impatrq/ojo_de_van_gogh/Docs/README.md

### Documentación

#### Este modulo esta divido de las siguientes partes:

* **Carpeta Tecnica**: dentro de esta carpeta esta la documentación técnica del proyecto. Aquí podemos encontrar la información de la *versión estable* del sistema y ver en mucho detalle que hace el proyecto, como lo hace y por que lo hace. Dentro de este archivo no hay ideas experimentales sino que **todo lo que se escribió esta comprobado que funciona**
* **Carpeta de Campo**: dentro de estar carpeta esta la documentación de campo. Aqui podemos encontrar la tracción del proyecto, teniendo la posibilidad de recapitular los errores que fueron surgiendo y como se solucionar
* **Entrevistas**: dentro de esta carpeta están las entrevistas que realizamos con personas con discapacidad visual para validar si nuestro producto es factible de tener una inserción en el mercado
