impatrq/ojo_de_van_gogh/Docs/Encuestas/Encuesta _Mitrovich.md

# Encuesta a Oscar Mitrovich

### Datos personales:

- Nombre: Oscar Alberto Mitrovich
- Edad: 62 años
- Actualmente es jubilado
- Estado civil: casado 
- Lugar: Quilmes Oeste

### Datos de la entrevista

- Cuando ya tenía algunos problemas de visión se opera en el 2015, llegó a tener mejoras pero después para el 2016 perdió la visión completa. 

- Para levantarse necesita ayuda de la esposa para poder desayunar excepto que ella le diga donde dejo el te y las galletitas
- Tiene marcado el microondas para saber calentar el te
- Cuando quiere buscar algo en el celular(previamente desbloqueado) cuando dice ok Google se da cuenta que ya puede decir algo a través de la vibración que larga el celular y ahí el dice pondme en Youtube ...
- La señora le sirve la comida en un bowl y de ahí el empieza a comer .
- Dice que el quedar ciego le cambió la vida.
- En algunas situaciones de pocas luces el puede llegar a tener momentos de ver algo medio borroso pero luego de unos minutos deja de ver.

### Preocupaciones de Oscar

1. Su mayor preocupación es el hecho de que no puede ser independiente y necesita mucho de su esposa para realizar algo
2. Busca videos sobre su problema para saber si hay alguna solución, costos y donde se realiza.
3. Tiene miedo de que cuando va a buscar en la heladera tirar algo. Aunque la esposa le dice donde tiene que buscar.
4. No puede desbloquear ni usar el celular solo ya que no tiene el asistente.
5. Cuando se mide la glucosa no sabe el valor que le da. La esposa le tiene que decir
6. La computadora no la usa porque no sabe como manejarse en esta. 
7. Le gustaba cocinar, tenia un emprendimiento que lo tuvo que dejar de hacer ya que le agarró esto.
8. Dice que ya es medio tarde para aprender Braille
9. No puede realizar compras, las hace su esposa con el hijo. 

### Cosas que le gustan a Oscar

- Le gusta hacer bicicleta en la casa
- Le gusta escuchar documentales, música, la televisión y la biblia 

### Opinión sobre el proyecto:

- Sobre el texto dijo que sería bastante útil ya que el tiene poco manejo con la tecnología 
- Propuso de que los estaría bueno poder reconocer los objetos para poder manejarse solo en la calle y no tener que depender de alguien
- Sobre el color le pareció interesante y dijo que sería una buena forma de suplir su ausencia.
