impatrq/ojo_de_van_gogh/Docs/Encuestas/Encuesta_Lucila.md

# Encuesta a Lucila

### Datos personales:

- Nombre: Lucila
- Edad: 28 años
- Trabajo: maestra de personas ciegas y con discapacidades múltiples
- Estado civil: casada con un hijo
- País que nació: Paraguay

### Enseñanza a chicos ciegos

- En los inicios del jardín y escuela primaria las personas con discapacidad visual hacen doble jornada: escuela de nivel y discapacidad.
- El braille se enseña en jardín a partir de 3 años: enseñándoles el sistema braille que son 2 columnas con 3 filas. Se enseña con los maples de huevos de 6 poniendo tapas o diferentes materiales. 
- Sala de 4: empiezan a hacer puntos y en preescolar empieza a darle forma. Se les enseña a hacer la inicial de sus nombres y vocales con el sistema braille.
- La maquina de braille es cara, hace 2 años 2000 dólares, lo que hace bastante difícil poder trabajar. Con el proyecto de cheques se facilitaba la compra  y después del 2018 se empezó a reducir y desde el año pasado que ya no esta. 
- Cuando se enseñan los colores se los muestran como un contenido. Por ejemplo en el color rojo le dicen que es de los colores primarios, y se relaciona con el fuego, el amor y les enseñan con que se combinan para la ropa. 
- Para enseñar a usar el teclado se referencian por la F y J y suelen marcar el enter y las direcciones. 

### Datos de la entrevista

- Tiene Glaucoma desde que nació: es una enfermedad del ojo que roba la visión de manera gradual.
- Hizo la escuela inicial con las 2 escuelas: etapa inicial y de discapacidad. 
- Trabaja en escuela especial enseñando braille y a chicos con discapacidad múltiple 
- Trabaja de 8:30 a 4:30. Tiene un hijo y es casada. 
- Usa los lectores de pantalla tanto en celular como en computadora
- Antes de la pandemia hacía las compras en el camino después de trabajar. En los almacenes como a conocen no necesita ayuda. En los supermercados pide ayuda y ella le dice el producto a la persona y esta le contesta los precios, maneja el changuito y la guía. 
- No le gusta hacer manualidades ni cocinar.  
- En el uso de la computadora usa las teclas guías : f y j. 
- Lectura en el celular, hay una biblioteca digital: tiflo libros. Manuales de primaria hay y libros. 

### Preocupaciones de Lucila

1. Tiene problemas para saber que dicen los tickets, cosas escritas. Billetes también es un gran problema. 
2. Necesita ayuda para los vencimientos de productos. 
3. Enseña los colores porque ellos tienen que saberlos porque viven en un mundo que se ve.
4. Problemas para saber que hay en las fotos: Google Lens te dice el contenido
5. Dijo que ella ve que en cuanto a niños hay pocas cosas como para mejorar su aprendizaje y que es difícil poder comprar una maquina braille por el elevado costo y la ausencia de ayuda de parte del Estado.
6. Se viste sola, pero los colores no los sabe distinguir  y le da duda e incógnita
7. En este contexto va a comprar el esposo porque si quiere ir ella necesita que alguien del supermercado o negocio la ayude.

### Cosas que le gustan a Lucila

- Le gusta escribir, pensar historias, investigar cosas, ver videos. 
- Le gusta leer audio libros.
- Le gusta mucho ayudar a personas con discapacidad múltiple. (Hace 2 años que empezó a hacer una magistratura de esto.)

### Programas que utilizan 

Los usan para reconocer PDFs e imágenes

- Google Lens: sirve mucho. 

- @ Voice Aloud. 

### Opinión sobre el proyecto:

- Sobre objeto, ella cree que serviría mas para nenes, ya que una persona que ya tiene varios años de experiencia ya distingue bastante bien los objetos
- Sobre textos: remarco que acá es un punto fuerte ya que una gran problemática es saber que dicen lo tickets, cosas escritas, billetes
- En cuanto al color le pareció algo bueno. No dijo palabras pero quedo asombrada
