impatrq/ojo_de_van_gogh/Docs/Encuestas/encuesta_monica.md

# Encuesta a Mónica:

### Datos personales:

- Edad: 58 años
- Nombre: Mónica
- Trabajo: no tuvo
- Estado civil: Soltera. Vive con su hermano.
- Ciudad: Quilmes (Ezpeleta)

### Datos de la entrevista

- Mónica perdió la visión parcial a los 14 años y luego de varios estudios y operaciones a los 24 años quedo ciega total. 
- En cuanto a su día a día ella se puede ubicar en espacios conocidos, se despierta y se hace el mate ella sola.
- Con las monedas suele poder identificarlas gracias a los diferentes dibujos y resaltados que tienen.
- Para identificar el color de la ropa lo realiza a través de que cada ropa que tiene es de un color distinto y se acuerda de la combinación de los colores(lo hace así porque así es como cree que esta bien)
- Para identificar las letras de la computadora tiene marcas en la A, V y Ñ y las demás se sabe de memoria las posiciones

### Preocupaciones  de Mónica:

1. No puede ir a comprar sola, ya que los supermercados no tienen ningún tipo de señalización ni información del costo del producto en braille ni nada. 
2. Problemas con la conexión a videos cuando hay mensajes de alerta en el que no se informa auditivamente de ese mensaje
3. No identifica los billetes ya que es complicado distinguir donde se encuentra el código braille y su identificación para cada billete en particular.  
4. A veces no puede realizar todas las comidas
6. No puede hacer podas debido a los riesgos pero le gustaría y lo realiza su hermano y ella le dice que tiene que hacer.
6. En cuanto a las monedas nuevas me dijo que vera como se va a ir dando cuenta para poder identificarlas. 

### Cosas que le gustan a Mónica:

- Le gusta tejer y hacer manualidades y dice que reconoce cuando esta mal a través del tacto y ya que ella lo aprendió antes de tener este problema.
- Le gusta cocinar y se da cuenta cuando la comida esta lista a través de que lo prueba y el espesor del agua. Para prepararla se maneja con tazas y/o cucharas llegando a estas a través del tacto.
- Le gusta ver videos, series y leer todo a través de la computadora.
