impatrq/ojo_de_van_gogh/Docs/Encuestas/Encuesta_OSVALDO_CIEGO_8-8.md

# Encuesta a Osvaldo

### Datos personales:

- Edad : 68 años
- Nombre : Osvaldo
- Trabajo : 45 Años en un Call Center. se jubilo a los 63
- Estado civil: Casado
- Ciudad: Berazategui (Sourigues)

### Datos de la entrevista:

- Osvaldo perdió la visión de un ojo a los 6 años, luego desarrollo visión monocular donde 1 ojo hace el trabajo de los dos. Su condición monocular lo llevo a que a los 33 años tenga que operarse y quedo ciego. Desde entonces aprendió en la ASAC cosas como:
  - Cocinar
  - Leer y escribir braille
  - Andar en bondi y caminar en la calle
- Osvaldo dijo que le gusta aprender cosas de tecnología como manejar computadoras y eso y que lo venia haciendo pero justo fue lo de la pandemia. 
- Dijo que tiene muchas expectativas de nuestro proyecto y que si tenemos algo que lo llamemos inmediato para ofrecérselo 

#### Preocupaciones de Osvaldo:

- Le molesta cuando las situaciones no tienen audios descriptivos. Por ejemplo cuando ve la tele a veces hay silencios y quiere saber que esta pasando pero no puede
- No le gusta que la sociedad no deje pasar al ciego cuando esta haciendo la fila en el banco
- Le gusta hacer los tramites pero no puede hacerlo solo a veces porque las facturas no vienen en braille
- Le molesta mucho que la gente piense que tener una discapacidad es motivo de vivir menos alegre la vida o frustrado 
- Le molesta no poder guiarse por el color de las cosas y simplemente decir que algo es tal color porque se lo dijeron y no tener un sentido asociado a eso(la vibración es importante)

#### Cosas que le gustan a Osvaldo:

- Escuchar la radio cuando no puede dormir
- Le gusta hacer chistes con que es ciego
- Le gusta sentirse independiente cuando hace cosas y no depender de su esposa
- Le sorprendería que haya alguna forma de sentir cuando habla de que esto es tal color ya que no puede sentir si es lindo o no
- Le gustaría poder leer todo y no limitarse a si esta en braille o no; o si es un audio libro
