impatrq/ojo_de_van_gogh/Docs/Carpeta_Tecnica/Diagrama_de_gantt.pdf

27

2

9 | 16 | 23 | 30
6 | 13 | 20 | 27
4 | 11 | 18 | 25

1

8 | 15 | 22 | 29
6 | 13 | 20 | 27
3 | 10 | 17 | 24 | 31
7 | 14 | 21 | 28
2/20 | 3/20 | 4/20 | 5/20 | 6/20 | 7/20 | 8/20 | 9/20
Ojo de Van Gogh | 0h | 2%
New Group | 0h | 0%
0h | 2%
Crear logo y Slogan
0 | 0%
Escribir Anteproyecto
0 | 30%
Entregar Anteproyecto
0 | 0%
Armar Presupuesto del Proyecto 0 100%
Entregar Presupuesto
0 | 0%
Tener toda la documentacion inicial ...
0 | 0%
Establecer entorno de trabajo de Go...
0 | 0%
Tomar foto y Analizarla por Bluetooth...
0 | 0%
Establecer entorno de trabajo de Ard...
0 | 0%
Crear una vibracion controlada por b...
0 | 0%
Diseñar sistema de Vibracion
0 | 0%
Establecer entorno de trabajo de Min...
0 | 0%
Tomar foto y Analizar por Bluetooth ...
0 | 0%
Crear sistema de alimentacion para l...
0 | 0%
Tener Raspberry funcionando por bl...
0 | 0%
Crear sistema de vibraciones de acu...
0 | 0%
Probar inteligencia artificial de raspb...
0 | 0%
Probar inteligencia artificial de rassp...
0 | 0%
Distribuir sistema de vibracion por v...
0 | 0%
Probar sistema completo
0 | 0%
Ojo de Van Gogh funcional a pulir los...
0 | 0%
Comenzar con la produccion de un v...
0 | 0%
Analisis y conclusiones de todo lo qu...
0 | 0%
Pulir Errores y revision total del sist...
0 | 0%
Descanso por vacaciones de invierno
0 | 0%
Investigar como agregar un mini par...
0 | 0%
Crear "modo aprendizaje"
0 | 0%
Vincular Modo Normal a Modo Apren...
0 | 0%
Empezar con la busqueda de sponso...
0 | 0%
Sacar conclusiones de la busqueda
0 | 0%
Iniciar busqueda numero 2 (Notas pe...
0 | 0%
Tener sistema listo y patrocinado cas...
0 | 0%
Crear Tecnica
0 | 0%
Crear guia de usuario
0 | 0%
Revisar Documentacion
0 | 0%
Traducir guia de usuario a Braille
0 | 0%
Revisar video promocional y mejorar...
0 | 0%
Crear Banner del proyecto
0 | 0%
Preparacion del grupo para olimpiad...
0 | 0%

Matias Gabriel Pierri
Matias Gabriel Pierri

Powered by TCPDF (www.tcpdf.org)
