impatrq/ojo_de_van_gogh/placa_electronica/raspberry_code/colores.csv

ID | Principal_color | CSS_name | HEX | R | G | B
0.0 | black | Negro | #000 | 0.1 | 0.1 | 0.1
1.0 | navy_blue | Azul Marino | #000080 | 0.1 | 0.1 | 128.0
2.0 | dark_blue | Azul Oscuro | #00008b | 0.1 | 0.1 | 139.0
3.0 | duke_blue | Azul Duque | #00009c | 0.1 | 0.1 | 156.0
4.0 | medium_blue | Azul Tenue | #0000cd | 0.1 | 0.1 | 205.0
5.0 | blue | Azul | #00f | 0.1 | 0.1 | 255.0
6.0 | phthalo_blue | Azul Ftalo | #000f89 | 0.1 | 15.0 | 137.0
7.0 | zaffre | Zaffre | #0014a8 | 0.1 | 20.0 | 168.0
8.0 | oxford_blue | Azul Oxford | #002147 | 0.1 | 33.0 | 71.0
9.0 | royal_blue_traditional | Azul Real (Tradicional) | #002366 | 0.1 | 35.0 | 102.0
10.0 | resolution_blue | Azul Resolucion | #002387 | 0.1 | 35.0 | 135.0
11.0 | imperial_blue | Azul Imperial | #002395 | 0.1 | 35.0 | 149.0
12.0 | cool_black | Negro Fresco | #002e63 | 0.1 | 46.0 | 99.0
13.0 | international_klein_blue | Azul Klein Internacional | #002fa7 | 0.1 | 47.0 | 167.0
14.0 | air_force_blue_usaf | Azul Fuerza Aerea (Usaf) | #00308f | 0.1 | 48.0 | 143.0
15.0 | prussian_blue | Azul Prusiano | #003153 | 0.1 | 49.0 | 83.0
16.0 | dark_midnight_blue | Azul Medianoche Oscuro | #036 | 0.1 | 51.0 | 102.0
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
