impatrq/ojo_de_van_gogh/placa_electronica/raspberry_code/codigos_auxiliares_ejemplos/detector_colores_query/Tabla_colores.csv

ID | Principal_color | CSS_name | HEX | R | G | B
0.0 | Green | Lima | 00 FF 00 | 0.1 | 255.0 | 0.1
1.0 | Green | Verde Primaveral | 00 FF 7F | 0.1 | 255.0 | 127.0
2.0 | Green | Verde Semi-Primaveral | 00 FA 9A | 0.1 | 250.0 | 154.0
3.0 | Green | Verde Primaveral | 00 80 00 | 0.1 | 128.0 | 0.1
4.0 | Green | Verde Oscuro | 00 64 00 | 0.1 | 100.0 | 0.1
5.0 | Cyan | Agua | 00 FF FF | 0.1 | 255.0 | 255.0
6.0 | Cyan | Cian | 00 FF FF | 0.1 | 255.0 | 255.0
7.0 | Cyan | Turquesa Oscuro | 00 CE D1 | 0.1 | 206.0 | 209.0
8.0 | Cyan | Azul Cadete | 00 8B 8B | 0.1 | 139.0 | 139.0
9.0 | Cyan | Verde Azuado | 00 80 80 | 0.1 | 128.0 | 128.0
10.0 | Blue | Azul Cielo | 00 BF FF | 0.1 | 191.0 | 255.0
11.0 | Blue | Azul | 00 00 FF | 0.1 | 0.1 | 255.0
12.0 | Blue | Azul Suave | 00 00 CD | 0.1 | 0.1 | 205.0
13.0 | Blue | Azul Oscuro | 00 00 8B | 0.1 | 0.1 | 139.0
14.0 | Blue | Azul Marino | 00 00 80 | 0.1 | 0.1 | 128.0
15.0 | Gray | Negro | 00 00 00 | 0.1 | 0.1 | 0.1
162.0 | Green | Verde Pantano | 00 AD 43 | 0.1 | 173.0 | 67.0
188.0 | Green | Verde UFO | 07 C5 69 | 7.0 | 197.0 | 105.0
140.0 | Black | Negro Chino | 14 14 14 | 20.0 | 20.0 | 20.0
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
