impatrq/ojo_de_van_gogh/placa_electronica/arduino_code/mindwave.h

void#ifndef mindwave_h
#define mindwave_h

#include "Arduino.h"

class Mindwave
{
    public:
        Mindwave(int _BAUDRATE, char _LED, char _Thesold_Eyeblink, char _EEG_AVG);
        byte ReadOneByte();
        void Small_Packet();
        void Big_Packet();
        void Onesec_Rawval_Fun();
        void Eye_Blink();
        void Calibrar_Sensor();
        void Esperar_al_mindwave();

    private:
    
        int BAUDRATE; 
        int ByteRead;
        char LED;
        char Thesold_Eyeblink;
        char EEG_AVG;
        long payloadDataS[5];
        long payloadDataB[32];
        byte checksum;
        byte generatedchecksum;
        unsigned int Raw_data;
        unsigned int Poorquality; 
        unsigned int Plength;
        unsigned int Eye_Enable ;
        unsigned int On_Flag ; 
        unsigned int Off_Flag = 1;
        unsigned int j, n;
        long Temp, Avg_Raw, Temp_Avg;
        long Calibracion_raw;
        long Umbral_de_parpadeo;
        int intento;
};
#endif
