impatrq/ojo_de_van_gogh/placa_electronica/arduino_code/codigos_auxiliares_ejemplo/bt-slave-json/Morse.h

#ifndef Morse_h
#define Morse_h
 
#include "Arduino.h"
 
    void punto();
    void raya();
    void blanco();
    void rojo();
    void marron();
    void naranja();
    void amarillo();
    void dorado();
    void beige();
    void violeta();
    void rosa();
    void purpura();
    void verde();
    void azul();
    void cyan();
    void plata();
    void gris();
    void negro();
     
#endif
